chradev/Adroid/assets/configs/42HB34F08AB.jpg

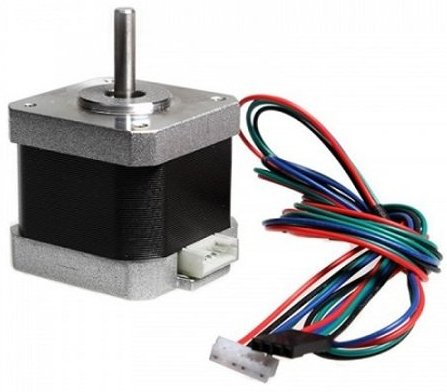
assets/configs/42HB34F08AB.jpg
