chradev/Adroid/assets/configs/ActiveBallJoint.jpg

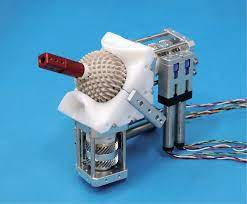
assets/configs/ActiveBallJoint.jpg
