chradev/Adroid/assets/configs/Example-of-sensors-used-in-robotics.png

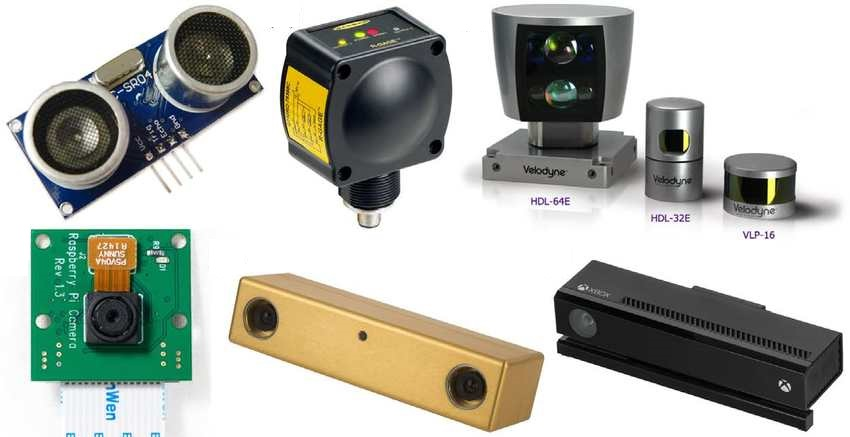
assets/configs/Example-of-sensors-used-in-robotics.png
