chradev/Adroid/assets/configs/NvidiaJetsonOrinNanoAdd-2.png

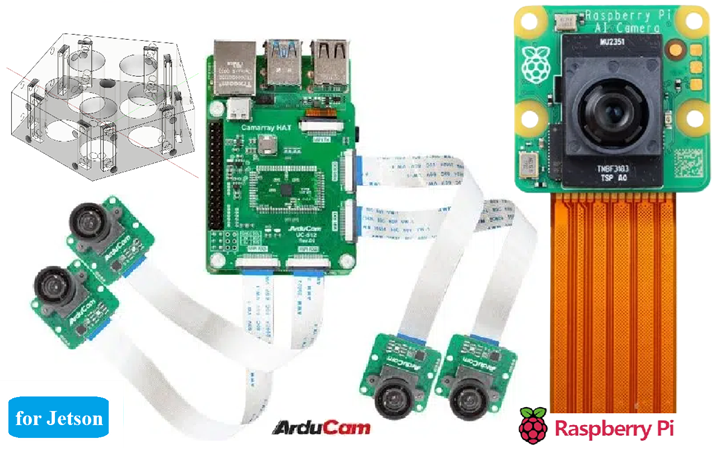
assets/configs/NvidiaJetsonOrinNanoAdd-2.png
