chradev/Adroid/assets/configs/NvidiaJetsonOrinNanoAdd.png

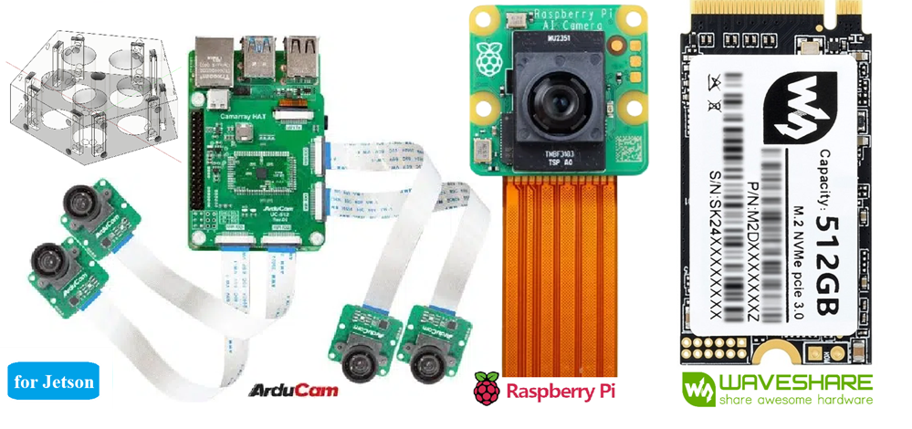
assets/configs/NvidiaJetsonOrinNanoAdd.png
