chradev/Adroid/assets/configs/RP2350-Stamp-and-Stamp-XL.jpg

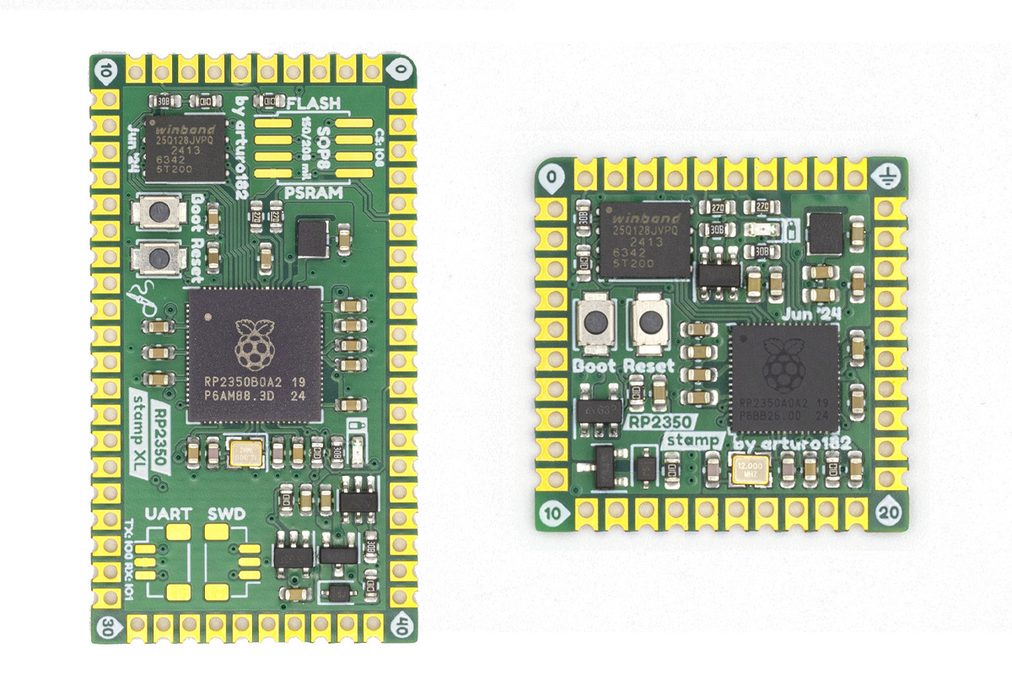
assets/configs/RP2350-Stamp-and-Stamp-XL.jpg
