chradev/Adroid/assets/configs/rpi-camera-3.jpg

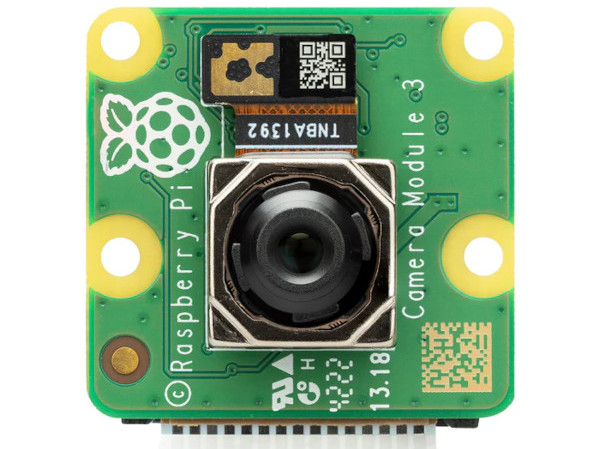
assets/configs/rpi-camera-3.jpg
