chradev/Adroid/assets/configs/RPi_5_active_cooler-1-768x768.jpg

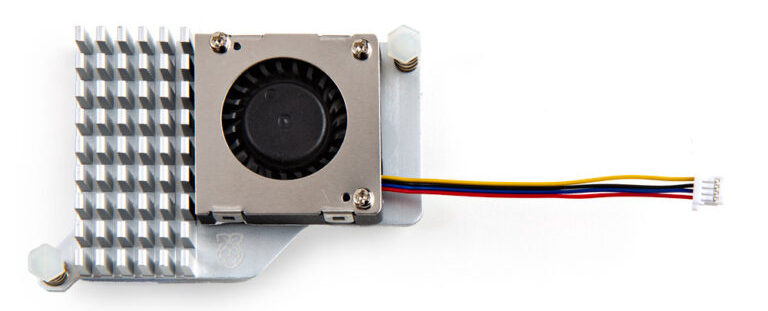
assets/configs/RPi_5_active_cooler-1-768x768.jpg
