chradev/Adroid/assets/configs/SK-NVME-512G-SSD.jpg

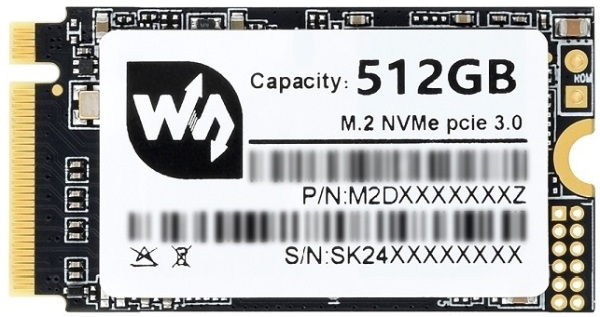
assets/configs/SK-NVME-512G-SSD.jpg
