chradev/Adroid/assets/configs/sk-nvme-2242-256g-ssd-m2.webp

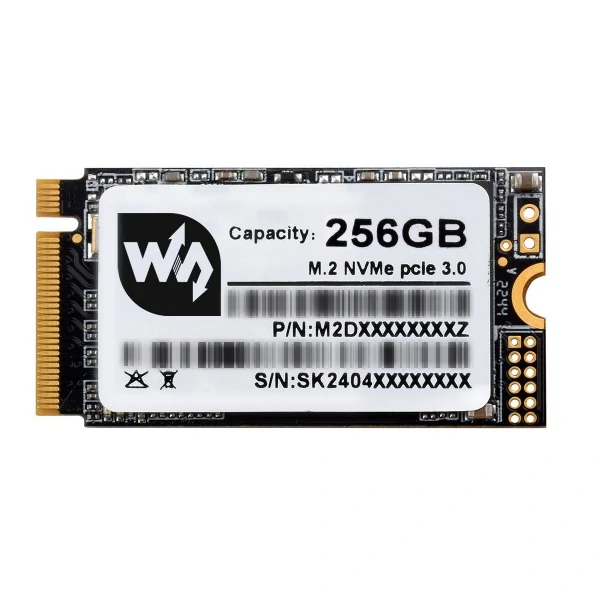
assets/configs/sk-nvme-2242-256g-ssd-m2.webp
