chradev/Adroid/assets/configs/SM-5VDC-DRV.jpg

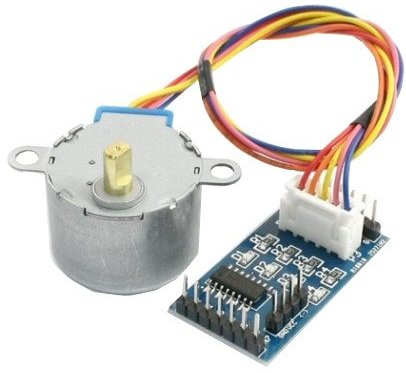
assets/configs/SM-5VDC-DRV.jpg
