chradev/Adroid/assets/configs/StrainGaugeOnPCB.png

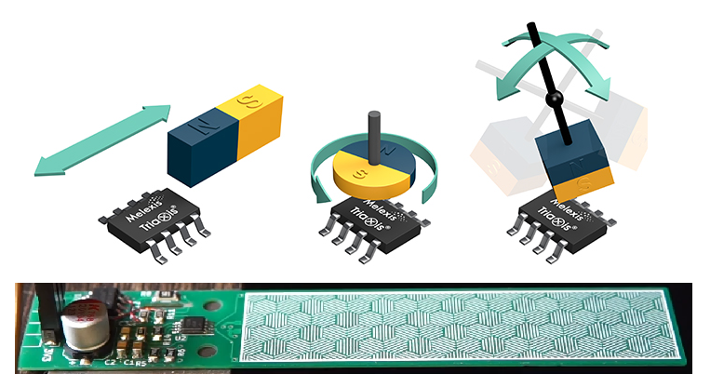
assets/configs/StrainGaugeOnPCB.png
