chradev/Adroid/assets/configs/usb3-card-reader.jpg

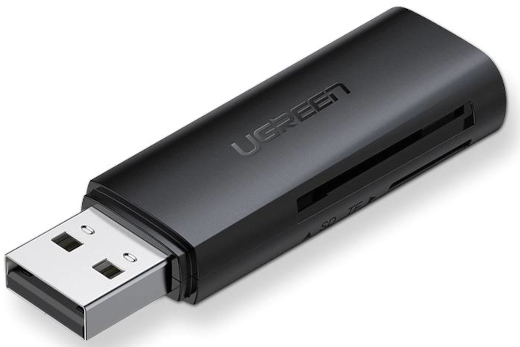
assets/configs/usb3-card-reader.jpg
