chradev/Adroid/assets/configs/usb3-sd-card-reader.png

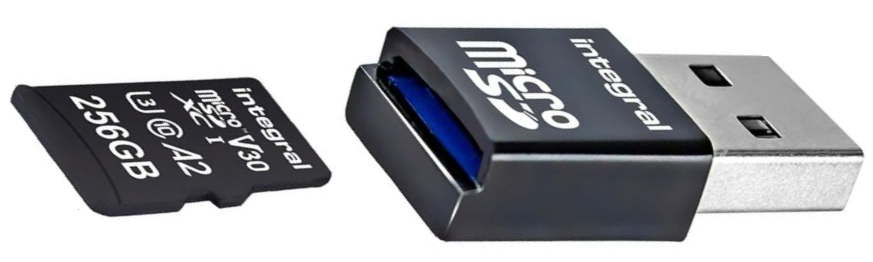
assets/configs/usb3-sd-card-reader.png
