chradev/Adroid/assets/configs/xiao-esp32s3-sense-7-768x768.webp

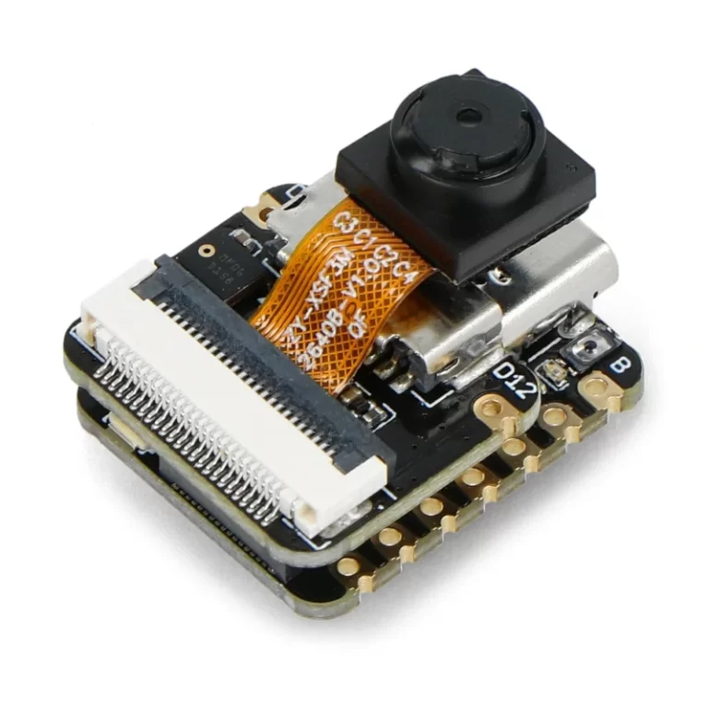
assets/configs/xiao-esp32s3-sense-7-768x768.webp
