chradev/Adroid/assets/theSmart-02.png

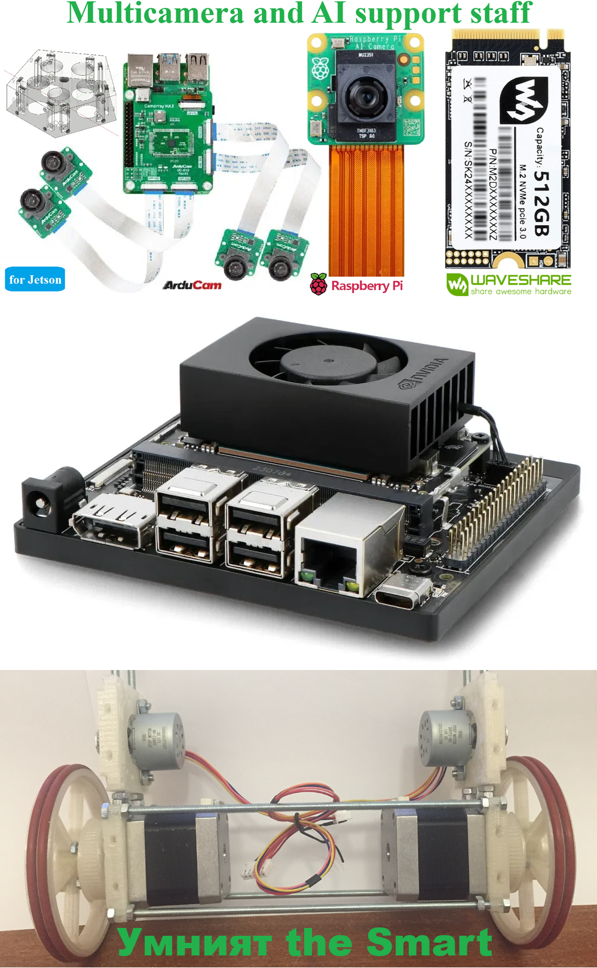
assets/theSmart-02.png
