chradev/Adroid/assets/theSmart-04.png

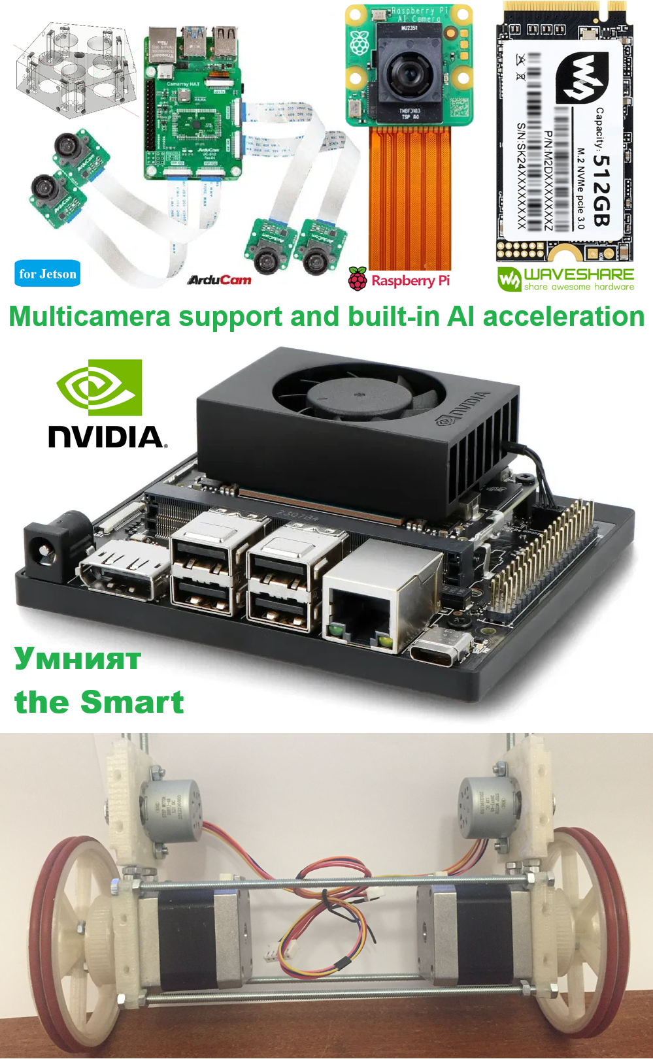
assets/theSmart-04.png
