chradev/Adroid/assets/theWide.png

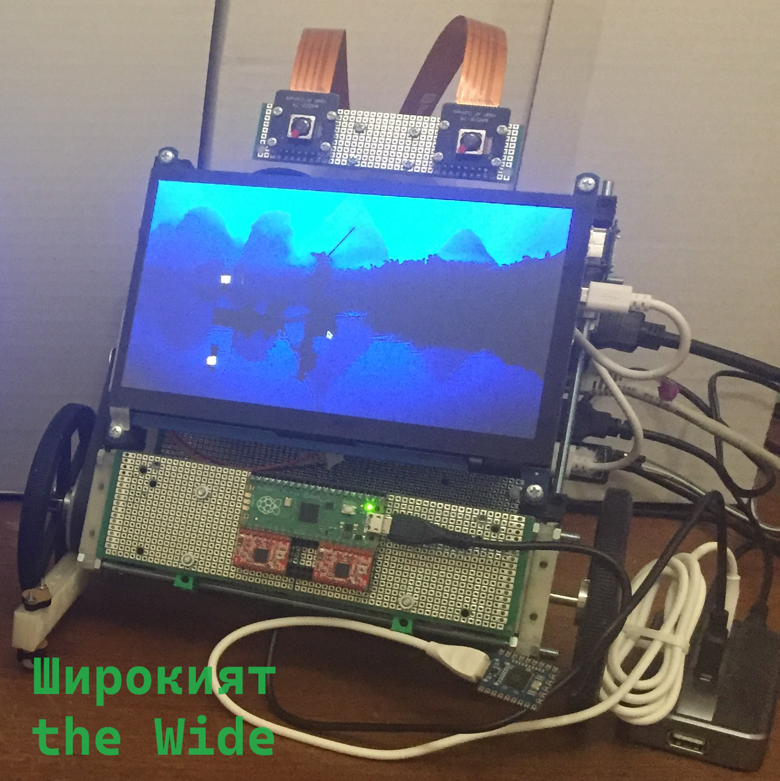
assets/theWide.png
